thlintw/clavert/pcb/clavert/clavert.kicad_sch

## KiCad design pcb/clavert/clavert.kicad_sch (2025-07-27)

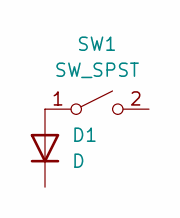
[picture p19: schematic clavert.kicad_sch]

Parts:
D1: D
SW1: SW_SPST

Connections:
unnamed: D1.2 (A), SW1.1 (A)
